masonandrewmann/MEAP/masons secret meap folder/Modulation/MEAP_Basic_FM/MEAP_Basic_FM.ino

/*
  Basic FM Patch
  
  Plays a constant sine wave at 440Hz modulates its frequency using another sine wave.
  Pot 1 controls the modulation oscillator's frequency.
  Pot 2 controls modulation depth.

  Mason Mann, CC0
 */

#include <MozziGuts.h>
#include <Oscil.h>
#include <mozzi_rand.h>
#include <mozzi_midi.h>
#include <Mux.h>
#include <SPI.h>
#include <tables/sin8192_int8.h> // loads sine wavetable

#define CONTROL_RATE 64 // Hz, powers of 2 are most reliable

using namespace admux;

Oscil<SIN8192_NUM_CELLS, AUDIO_RATE> carrierOsc(SIN8192_DATA);
Oscil<SIN8192_NUM_CELLS, AUDIO_RATE> modulatorOsc(SIN8192_DATA);

Q16n16 modDepth = 0;

// variables for potentiometers
int potVals[] = {0, 0};

void setup(){
  Serial.begin(115200);
  pinMode(34, INPUT);
  startMozzi(CONTROL_RATE);
  carrierOsc.setFreq(440); //set frequency of carrier oscillator
  modulatorOsc.setFreq(440); //set frequency of modulation oscillator
}


void loop(){
  audioHook();
}


void updateControl(){
  readPots(); // reads potentiometers
  modulatorOsc.setFreq((float)map(potVals[0], 0, 4095, 1, 1000)); // set mod oscillator range to 1->1000Hz
  modDepth = Q7n0_to_Q7n8(map(potVals[1], 0, 4095, 0, 127)); // convert mod depth to fixed point signed int between 0 and 127
}


int updateAudio(){
  Q15n16 modulation = modDepth * modulatorOsc.next() >> 8; // calculate mod depth in 15n16 signed int
  return MonoOutput::from8Bit(carrierOsc.phMod(modulation * 4)); // scale by factor of 4 and apply phase mod to carrier oscillator 
}

void readPots(){
  mozziAnalogRead(0);
  potVals[0] = mozziAnalogRead(39);
  
  mozziAnalogRead(1);
  potVals[1] = mozziAnalogRead(36);
}
