masonandrewmann/MEAP/Meap.h

/*
  Meap.h - Library accompanying MEAP boards.
  Created by Mason Mann, January 24, 2024.
*/
#ifndef MEAP_H_
#define MEAP_H_

#include "MozziConfigValues.h"
#define ESP_SAMPLE_SIZE 4 // 2 * sizeof(int16_t)

#ifndef MOZZI_AUDIO_RATE
#define MOZZI_AUDIO_RATE 32768
#endif

#ifndef MOZZI_CONTROL_RATE
#define MOZZI_CONTROL_RATE 64
#endif

#define MOZZI_AUDIO_MODE MOZZI_OUTPUT_EXTERNAL_CUSTOM
#define MOZZI_AUDIO_BITS 16
#define MOZZI_PDM_RESOLUTION 8

#ifndef MOZZI_AUDIO_CHANNELS
#define MOZZI_AUDIO_CHANNELS MOZZI_STEREO
#endif

#include "Arduino.h"
#include <Mozzi.h>

#include "driver/i2s_std.h"
// // I2S communication with SGTL5000 Audio Codec

#include <MIDI.h> // Arduino Midi library https://github.com/FortySevenEffects/arduino_midi_library

#include "Meap_classes.h"
// include all mozzi modules
#include <mozzi_midi.h>
#include <mozzi_fixmath.h>
#include <mozzi_rand.h>
#include <ADSR.h>
#include <AudioDelay.h>
#include <AudioDelayFeedback.h>
#include <AutoMap.h>
#include <AutoRange.h>
#include <CapPoll.h>
// #include <CircularBuffer.h> // not included because it causes a redeclaration error, should have an #ifdef clause like rest of modules
#include <ControlDelay.h>
#include <DCfilter.h>
#include <Ead.h>
#include <EventDelay.h>
#include <IntMap.h>
#include <Line.h>
#include <Metronome.h>
#include <ResonantFilter.h>
#include <Oscil.h>
#include <PDResonant.h>
#include <Phasor.h>
#include <Portamento.h>
#include <RCpoll.h>
#include <ReverbTank.h>
#include <RollingAverage.h>
#include <Sample.h>
#include <SampleHuffman.h>
#include <Smooth.h>
#include <StateVariable.h>
#include <WaveFolder.h>
#include <WavePacket.h>
#include <WavePacketSample.h>
#include <WaveShaper.h>

#include <meap_modules/tools/midi_notes.h>

// ---- dependencies ----
#include <dependencies/LinkedList/LinkedList.h>

// ---- meap extensions to mozzi objects ----
#include <meap_mozzi/mSample.h>
#include <meap_mozzi/mOscil.h>
#include <meap_mozzi/mPortamento.h>
#include <meap_mozzi/mEad.h>

// clutter
#include <meap_modules/clutter/mSampler.h>

// #include <meap_modules/clutter/mSamplerVoice.h>
// #include <meap_modules/clutter/mSamplerPoly.h>
// #include <meap_modules/clutter/mBasicFM.h>
// #include <meap_modules/clutter/mBasicFMPoly.h>
#include <meap_modules/clutter/mGrainGenerator.h>
#include <meap_modules/clutter/mGrainCloud.h>
#include <meap_modules/clutter/mSampleGrainGenerator.h>
#include <meap_modules/clutter/mSampleGrainCloud.h>
// #include <meap_modules/clutter/mGuitarPoly.h>
// #include <meap_modules/clutter/mFM2Voice.h>
// #include <meap_modules/clutter/mFM2Poly.h>
// #include <meap_modules/clutter/mWavetableSynth.h>
// #include <meap_modules/clutter/mOscBank.h>
// #include <meap_modules/clutter/mRealSamplerPoly.h>
// #include <meap_modules/clutter/mChopper.h>

// -------------------- MEAP DSP --------------------

// ---- TOOLS ----
#include <meap_modules/tools/fast_pow2.h>
#include <meap_modules/tools/mRandomDistribution.h>
#include <meap_modules/tools/mEventDelayMicros.h>
// #include <meap_modules/tools/mSD.h>
// #include <meap_modules/tools/mPlaySD16.h>
// #include <meap_modules/tools/mPlaySD8.h>

// ---- DSP ----
#include <meap_modules/dsp/mFIR.h>
#include <meap_modules/dsp/mIIR.h>
#include <meap_modules/dsp/mNaturalComb.h>
#include <meap_modules/dsp/mFeedbackComb.h>
#include <meap_modules/dsp/mFeedforwardComb.h>
#include <meap_modules/dsp/mNaturalComb.h>
#include <meap_modules/dsp/mOnePoleLPF.h>
#include <meap_modules/dsp/mSchroederAllpass.h>
#include <meap_modules/dsp/mDelayLine.h>
#include <meap_modules/dsp/mRingz.h>
#include <meap_modules/dsp/mResonz.h>

// ---- EFFECTS ----
#include <meap_modules/effects/mSchroederReverb.h>
#include <meap_modules/effects/mPlateReverb.h>
#include <meap_modules/effects/mDigitalDelay.h>
#include <meap_modules/effects/mBitcrusher.h>
#include <meap_modules/effects/mFlanger.h>
#include <meap_modules/effects/mChorus.h>
#include <meap_modules/effects/mAnalogDelay.h>
#include <meap_modules/effects/mBufferOverride.h>

// ---- GENERATORS ----
#include <meap_modules/generators/mSineLFO.h>
#include <meap_modules/generators/mOperator.h>
#include <meap_modules/generators/mDust.h>
#include <meap_modules/generators/mWavetable.h>
#include <meap_modules/generators/mNoise.h>
#include <meap_modules/generators/mEnvSection.h>
#include <meap_modules/generators/mEnvelope.h>

// ---- INSTRUMENTS ----

#include <meap_modules/instruments/mInstrument.h>

#include <meap_modules/instruments/mFM4Voice.h>
#include <meap_modules/instruments/mFM4Instrument.h>

#include <meap_modules/instruments/mSubSynthVoice.h>
#include <meap_modules/instruments/mSubSynthInstrument.h>

#include <meap_modules/instruments/mStringSynthVoice.h>
#include <meap_modules/instruments/mStringSynthInstrument.h>

#include <meap_modules/instruments/mStringVoice.h>
#include <meap_modules/instruments/mStringInstrument.h>

#include <meap_modules/instruments/mPopVoice.h>
#include <meap_modules/instruments/mPopInstrument.h>

#include <meap_modules/instruments/mMarimbaVoice.h>
#include <meap_modules/instruments/mMarimbaInstrument.h>

// #include <meap_modules/instruments/mSamplerInstrument.h>

// nonstandard instruments

#include <meap_modules/instruments/mDrumRack.h>

#include <meap_modules/instruments/mDrumRackInstrument.h>

#include <meap_modules/instruments/mRompler.h>

// ---- COMPOSITION ----

#include <meap_modules/composition/mMML.h>
#include <meap_modules/composition/mTransitionTable.h>

// ---- WINDOWS ----
// adapted from pippi https://git.sr.ht/~hecanjog/pippi
#include <windows/WIN_BART.h>
#include <windows/WIN_BLACK.h>
#include <windows/WIN_COS.h>
#include <windows/WIN_GAUSS.h>
#include <windows/WIN_GAUSSIN.h>
#include <windows/WIN_GAUSSOUT.h>
#include <windows/WIN_HAMM.h>
#include <windows/WIN_HANN.h>
#include <windows/WIN_HANNIN.h>
#include <windows/WIN_HANNOUT.h>
#include <windows/WIN_NONE.h>
#include <windows/WIN_PLUCKIN.h>
#include <windows/WIN_PLUCKOUT.h>
#include <windows/WIN_RSAW.h>
#include <windows/WIN_SAW.h>
#include <windows/WIN_SINC.h>
#include <windows/WIN_SINE.h>
#include <windows/WIN_SINEIN.h>
#include <windows/WIN_SINEOUT.h>
#include <windows/WIN_TRI.h>

const uint16_t *MEAP_WINDOWS[] = { //  20 windows
    WIN_BART_DATA,
    WIN_BLACK_DATA,
    WIN_COS_DATA,
    WIN_GAUSS_DATA,
    WIN_GAUSSIN_DATA,
    WIN_GAUSSOUT_DATA,
    WIN_HAMM_DATA,
    WIN_HANN_DATA,
    WIN_HANNIN_DATA,
    WIN_HANNOUT_DATA,
    WIN_NONE_DATA,
    WIN_PLUCKIN_DATA,
    WIN_PLUCKOUT_DATA,
    WIN_RSAW_DATA,
    WIN_SAW_DATA,
    WIN_SINC_DATA,
    WIN_SINE_DATA,
    WIN_SINEIN_DATA,
    WIN_SINEOUT_DATA,
    WIN_TRI_DATA};

// ---- WAVETABLES ----
#include <wavetables/WT_SAW.h>
#include <wavetables/WT_SINE.h>
#include <wavetables/WT_SQUARE.h>
#include <wavetables/WT_TRI.h>

i2s_chan_handle_t tx_handle;
i2s_chan_handle_t rx_handle;

// MOZZI output buffer
bool _esp32_can_buffer_next = true; // initialize to true
int16_t _esp32_prev_sample[2];

int16_t meap_input_frame[2];

inline bool esp32_tryWriteSample()
{
    size_t bytes_written;
    i2s_channel_write(tx_handle, &_esp32_prev_sample, 4, &bytes_written, 0); // 4 = 2 * sizeof(int16_t)
    return (bytes_written != 0);
}

inline void audioOutput(const AudioOutput f)
{
    _esp32_prev_sample[0] = f.l();
    _esp32_prev_sample[1] = f.r();

    _esp32_can_buffer_next = esp32_tryWriteSample();

    // audio input
    size_t bytes_read;
    i2s_channel_read(rx_handle, &meap_input_frame, 4, &bytes_read, 0);
}

inline bool canBufferAudioOutput()
{
    if (_esp32_can_buffer_next)
    {
        return true;
    }
    _esp32_can_buffer_next = esp32_tryWriteSample();
    return _esp32_can_buffer_next;
}

#endif // MEAP_H_
