masonandrewmann/MEAP/meap_modules/clutter/mFM2Poly.h

#ifndef MFM2POLY_H_
#define MFM2POLY_H_

#include <Meap.h>
#include <tables/sin8192_int8.h> // table for Oscils to play
#include <dependencies/LinkedList/LinkedList.h>

template <uint32_t mNUM_CELLS = SIN8192_NUM_CELLS, bool FILTER_ACTIVE = false, uint16_t mPOLYPHONY = 4, class T = int8_t>
class mFM2Poly
{
public:
    mFM2Poly(const int8_t *TABLE_NAME, uint8_t *midi_table_name)
    {
        init(TABLE_NAME, midi_table_name);
    };

    mFM2Poly(const int8_t *TABLE_NAME)
    {
        init(TABLE_NAME, NULL);
    };

    mFM2Poly()
    {
        init(SIN8192_DATA, NULL);
    }

    void init(const int8_t *TABLE_NAME, uint8_t *midi_table_name)
    {
        for (uint16_t i = 0; i < mPOLYPHONY; i++)
        {
            voices[i].init(TABLE_NAME);
            free_voices_.unshift(i); // add all voices to voice queue
        }
        curr_voice_ = 0;
        midi_table_name_ = midi_table_name;
        playing_ = false;

        message_type_ = 0;
        data1_ = 0;
        data2_ = 0;
        time_ = 0;

        pulse_counter_ = 0;
    }

    void begin()
    {
        // start_time = millis();
        stop();
        playing_ = true;
        current_midi_address_ = midi_table_name_;
        pulse_counter_ = 0;
        message_type_ = current_midi_address_[0];
        data1_ = current_midi_address_[1];
        data2_ = current_midi_address_[2];
        time_ = (current_midi_address_[3] << 8) + current_midi_address_[4];
    }

    void stop()
    {
        // send noteoffs to everything
        playing_ = false;
        for (uint16_t i = 0; i < mPOLYPHONY; i++)
        {
            voices[i].noteOff();
        }
        flush();
    }

    void updateMidi()
    {
        if (playing_)
        {
            pulse_counter_ += 1;
            while (pulse_counter_ >= time_)
            {
                switch (message_type_) // notes are indexed from 0 on sample_bank starting from C-1 (0)
                {
                case 0x80: // note off
                    noteOff(data1_);
                    break;
                case 0x90: // note on
                    if (data1_ != 127)
                    {
                        noteOn(data1_, data2_);
                    }
                    break;
                case 255: // end of file
                    playing_ = false;
                    return;
                    break;
                }
                current_midi_address_ += 5;
                pulse_counter_ = 0;
                message_type_ = current_midi_address_[0];
                data1_ = current_midi_address_[1];
                data2_ = current_midi_address_[2];
                time_ = (current_midi_address_[3] << 8) + current_midi_address_[4];
            }
        }
    }

    bool isPlaying()
    {
        return playing_;
    }

    void noteOn(uint16_t note, float vel)
    {
        if (free_voices_.size() > 0)
        {
            curr_voice_ = free_voices_.shift(); // remove head element and return it!
        }
        else
        {
            return; // no free voices, move along...
        }

        voices[curr_voice_].noteOn(note, vel);

        // store note in pressed notes queue
        MeapNoteAndVoice *my_note = new MeapNoteAndVoice;
        my_note->note_num = note;
        my_note->voice_num = curr_voice_;
        nonfree_voices_.add(my_note);
    }

    void noteOff(uint16_t note)
    {

        uint8_t num_nonfree_voices = nonfree_voices_.size();
        for (uint8_t i = 0; i < num_nonfree_voices; i++)
        {
            if (nonfree_voices_.get(i)->note_num == note)
            {
                uint8_t voice_num = nonfree_voices_.get(i)->voice_num; // voice num of note to turn off
                voices[voice_num].noteOff();
                free_voices_.add(voice_num);     // re-add voice to free queue
                delete (nonfree_voices_.get(i)); // delete voice from pressed queue
                nonfree_voices_.remove(i);       // remove freed voice from pressed queue
                return;
            }
        }
    }

    void flush()
    {
        nonfree_voices_.clear();
        free_voices_.clear();
        for (uint8_t i = 0; i < mPOLYPHONY; i++)
        {
            free_voices_.unshift(i); // add all voices to voice queue
            voices[i].noteOff();
        }
    }

    void setModADLevels(uint32_t a_l, uint32_t d_l)
    {
        for (uint16_t i = 0; i < mPOLYPHONY; i++)
        {
            voices[i].setModADLevels(a_l, d_l);
        }
    }

    void setCarrierADLevels(uint32_t a_l, uint32_t d_l)
    {
        for (uint16_t i = 0; i < mPOLYPHONY; i++)
        {
            voices[i].setCarrierADLevels(a_l, d_l);
        }
    }

    void setAlgorithm(int alg)
    {
        for (uint16_t i = 0; i < mPOLYPHONY; i++)
        {
            voices[i].setAlgorithm(alg);
        }
    }

    void setModTimes(uint32_t a_t, uint32_t d_t, uint32_t s_t, uint32_t r_t)
    {
        for (uint16_t i = 0; i < mPOLYPHONY; i++)
        {
            voices[i].setModTimes(a_t, d_t, s_t, r_t);
        }
    }

    void setCarrierTimes(uint32_t a_t, uint32_t d_t, uint32_t s_t, uint32_t r_t)
    {
        for (uint16_t i = 0; i < mPOLYPHONY; i++)
        {
            voices[i].setCarrierTimes(a_t, d_t, s_t, r_t);
        }
    }

    void setRatio(float mod_ratio)
    {
        for (uint16_t i = 0; i < mPOLYPHONY; i++)
        {
            voices[i].setRatio(mod_ratio);
        }
    }

    void setModTable(const T *TABLE_NAME)
    {
        for (uint16_t i = 0; i < mPOLYPHONY; i++)
        {
            voices[i].setModTable(TABLE_NAME);
        }
    }

    void setCarrierTable(const T *TABLE_NAME)
    {
        for (uint16_t i = 0; i < mPOLYPHONY; i++)
        {
            voices[i].setCarrierTable(TABLE_NAME);
        }
    }

    // 0-255
    void setFMAmount(int fm_amount)
    {
        for (uint16_t i = 0; i < mPOLYPHONY; i++)
        {
            voices[i].setFMAmount(fm_amount);
        }
    }

    void setCutoff(uint16_t cutoff_val)
    {
        for (uint16_t i = 0; i < mPOLYPHONY; i++)
        {
            voices[i].setCutoff(cutoff_val);
        }
    }

    void setResonance(uint16_t resonance_val)
    {
        for (uint16_t i = 0; i < mPOLYPHONY; i++)
        {
            voices[i].setResonance(resonance_val);
        }
    }

    void setFilterEnvAmount(uint16_t f_amt)
    {
        for (uint16_t i = 0; i < mPOLYPHONY; i++)
        {
            voices[i].setFilterEnvAmount(f_amt);
        }
    }

    void setFilterEnvTimes(uint32_t a_, uint32_t d_, uint32_t s_, uint32_t r_)
    {
        for (uint16_t i = 0; i < mPOLYPHONY; i++)
        {
            voices[i].setFilterEnvTimes(a_, d_, s_, r_);
        }
    }

    void setFilterAttackTime(uint32_t f_a)
    {
        for (uint16_t i = 0; i < mPOLYPHONY; i++)
        {
            voices[i].setFilterAttackTime(f_a);
        }
    }

    void setFilterDecayTime(uint32_t f_d)
    {
        for (uint16_t i = 0; i < mPOLYPHONY; i++)
        {
            voices[i].setFilterDecayTime(f_d);
        }
    }

    void setFilterReleaseTime(uint32_t f_r)
    {
        for (uint16_t i = 0; i < mPOLYPHONY; i++)
        {
            voices[i].setFilterReleaseTime(f_r);
        }
    }

    void setFilterSustainLevel(uint16_t level)
    {
        for (uint16_t i = 0; i < mPOLYPHONY; i++)
        {
            voices[i].setFilterSustainLevel(level);
        }
    }

    void setFilterType(uint16_t f_t)
    {
        for (uint16_t i = 0; i < mPOLYPHONY; i++)
        {
            voices[i].setFilterType(f_t);
        }
    }

    void update()
    {
        for (uint16_t i = 0; i < mPOLYPHONY; i++)
        {
            voices[i].update();
        }
    }

    int32_t next()
    {
        int32_t out_sample = 0;
        for (uint16_t i = 0; i < mPOLYPHONY; i++)
        {
            out_sample += voices[i].next();
        }

        return out_sample;
    }

    uint8_t *current_midi_address_;

    mFM2Voice<mNUM_CELLS, FILTER_ACTIVE, T> voices[mPOLYPHONY];

    // CLASS VARIABLES
    LinkedList<int16_t> free_voices_;
    LinkedList<MeapNoteAndVoice *> nonfree_voices_;

    uint16_t curr_voice_;

    // reading midi file
    uint8_t *midi_table_name_;

    uint64_t pulse_counter_;

    bool playing_;

    // last midi message
    uint8_t message_type_;
    uint8_t data1_;
    uint8_t data2_;
    uint16_t time_;
};

#endif // MFM2POLY_H_
