masonandrewmann/MEAP/masons secret meap folder/MARNIE/4YRS/MARNIE_D_4YRS/patterns.h

#define NUM_PATTERNS 8
#define NUM_DRUMS 8

int sample_pattern[NUM_PATTERNS][NUM_DRUMS][32] = 
  {
    {
      {1, 0, 0, 0, 1, 0, 0, 0,  1, 0, 0, 0, 1, 0, 0, 0,   1, 0, 0, 0, 1, 0, 0, 0,  1, 0, 0, 0, 1, 0, 0, 0},
      {0, 0, 0, 0, 1, 0, 0, 0,  0, 0, 0, 0, 1, 0, 0, 0,   0, 0, 0, 0, 1, 0, 0, 0,  0, 0, 0, 0, 1, 0, 0, 0},
      {0, 0, 1, 1, 0, 0, 1, 0,  0, 0, 1, 0, 0, 0, 1, 0,   0, 0, 1, 1, 0, 0, 1, 0,  0, 0, 1, 0, 0, 0, 1, 0},
      {0, 0, 0, 0, 0, 0, 0, 0,  0, 0, 0, 0, 0, 0, 0, 0,   0, 0, 0, 0, 0, 0, 0, 0,  0, 0, 0, 0, 0, 0, 0, 0},
      {0, 0, 0, 0, 0, 0, 0, 0,  0, 0, 0, 0, 0, 0, 1, 0,   0, 0, 0, 0, 0, 0, 0, 0,  0, 0, 0, 0, 0, 0, 1, 0},
      {0, 0, 0, 0, 0, 0, 0, 0,  0, 0, 0, 0, 0, 0, 0, 0,   0, 0, 0, 0, 0, 0, 0, 0,  0, 0, 0, 0, 0, 0, 0, 1},
      {0, 0, 0, 0, 0, 0, 0, 0,  0, 0, 0, 0, 0, 0, 0, 0,   0, 0, 0, 0, 0, 0, 0, 0,  0, 0, 0, 0, 0, 0, 0, 0},
      {0, 0, 0, 0, 0, 0, 0, 0,  0, 0, 0, 0, 0, 0, 0, 0,   0, 0, 0, 0, 0, 0, 0, 0,  0, 0, 0, 0, 0, 0, 0, 0},
    },

    {
      {1, 0, 0, 1, 0, 0, 0, 0,  1, 0, 1, 1, 0, 0, 0, 0,   1, 0, 0, 1, 0, 0, 0, 0,  1, 0, 1, 1, 0, 0, 0, 0},
      {0, 0, 0, 0, 1, 1, 0, 1,  0, 0, 0, 0, 1, 0, 1, 0,   0, 0, 0, 0, 1, 1, 0, 1,  0, 0, 0, 0, 1, 0, 1, 0},
      {0, 0, 1, 0, 1, 0, 1, 0,  1, 0, 1, 0, 1, 0, 1, 1,   0, 0, 1, 0, 1, 0, 1, 0,  1, 0, 1, 0, 1, 0, 1, 1},
      {0, 1, 0, 0, 0, 0, 0, 0,  0, 1, 0, 0, 0, 0, 0, 0,   0, 1, 0, 0, 0, 0, 0, 0,  0, 1, 0, 0, 0, 0, 0, 0},
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
      {0, 0, 0, 0, 0, 0, 0, 0,  0, 0, 0, 0, 1, 0, 0, 0,   0, 0, 0, 0, 0, 0, 0, 0,  0, 0, 0, 0, 1, 0, 0, 0},
      {0, 0, 0, 0, 0, 0, 0, 0,  0, 0, 0, 0, 0, 0, 0, 0,   0, 0, 0, 0, 0, 0, 0, 0,  0, 0, 0, 0, 0, 0, 0, 0},
    }
  };
