masonandrewmann/MEAP/meap_modules/instruments/mDrumRack.h

#ifndef MEAP_DRUMRACK_H_
#define MEAP_DRUMRACK_H_

#include <meap_mozzi/mSample.h>

template <uint64_t mMAX_SAMPLE_LENGTH, uint8_t mNUM_SAMPLES, class T = int8_t>
class mDrumRack
{
public:
    mDrumRack(const T **sample_list, uint32_t *sample_lengths, uint8_t *midi_table_name = NULL)
    {
        sample_list_ = sample_list;
        sample_lengths_ = sample_lengths;

        midi_table_name_ = midi_table_name;

        playing_ = false;

        message_type_ = 0;
        data1_ = 0;
        data2_ = 0;
        time_ = 0;

        pulse_counter_ = 0;

        default_freq_ = (float)AUDIO_RATE / (float)mMAX_SAMPLE_LENGTH;

        for (int i = mNUM_SAMPLES; --i >= 0;)
        {
            velocity_[i] = 32385; // 127 * 255
            sample_gain_[i] = 255;
            sample_bank_[i].setTable(sample_list_[i]);
            sample_bank_[i].setEnd(sample_lengths[i]);
            sample_bank_[i].setFreq(default_freq_);
        }

        if (sizeof(T) == sizeof(int16_t))
        {
            shift_val_ = 15; // 8 bits down for sample birate + 7 bits for velocity
        }
        else
        {
            shift_val_ = 7; // just 7 bits down for velocity
        }
    };
    void midiStart()
    {
        // start_time = millis();
        playing_ = true;
        current_address_ = midi_table_name_;
        pulse_counter_ = 0;
        message_type_ = current_address_[0];
        data1_ = current_address_[1];
        data2_ = current_address_[2];
        time_ = (current_address_[3] << 8) + current_address_[4];
    }

    void midiStop()
    {
        // stop all notes
        playing_ = false;
        for (int i = mNUM_SAMPLES; --i >= 0;)
        {
            sample_bank_[i].stop();
        }
    }

    void flush()
    {
        for (int i = mNUM_SAMPLES; --i >= 0;)
        {
            sample_bank_[i].stop();
        }
    }

    void updateMidi()
    {
        if (playing_)
        {
            pulse_counter_ += 1;
            while (pulse_counter_ >= time_)
            {

                switch (message_type_) // notes are indexed from 0 on sample_bank starting from C-1 (0)
                {
                // case 0x80: // note off
                //     break;
                case 0x90: // note on
                    if (data1_ != 127)
                    {
                        noteOn(data1_, data2_);
                    }
                    break;
                case 255: // end of file
                    playing_ = false;
                    return;
                    break;
                }
                pulse_counter_ = 0;

                current_address_ += 5;
                message_type_ = current_address_[0];
                data1_ = current_address_[1];
                data2_ = current_address_[2];
                time_ = (current_address_[3] << 8) + current_address_[4];
            }
        }
    }

    bool isPlaying()
    {
        return playing_;
    }

    void noteOn(uint16_t sample_num, int vel, float speed)
    {
        sample_bank_[sample_num].setFreq(speed * default_freq_);
        sample_bank_[sample_num].start();
        velocity_[sample_num] = vel * sample_gain_[sample_num];
    }

    void noteOn(uint16_t sample_num, int vel = 127)
    {
        sample_bank_[sample_num].start();
        velocity_[sample_num] = vel * sample_gain_[sample_num];
    }

    void noteOff(uint16_t sample_num)
    {
        sample_bank_[sample_num].stop();
    }

    void setSampleVolume(uint16_t sample_num, int volume)
    {
        sample_gain_[sample_num] = volume;
    }

    int32_t next()
    {
        uint64_t output_sample = 0;
        for (int i = mNUM_SAMPLES; --i >= 0;)
        {
            output_sample += (sample_bank_[i].next() * velocity_[i]) >> shift_val_;
        }
        return output_sample;
    }

    // CLASS VARIABLES

    mSample<mMAX_SAMPLE_LENGTH, AUDIO_RATE, T> sample_bank_[mNUM_SAMPLES];
    int velocity_[mNUM_SAMPLES];

    const T **sample_list_;
    uint32_t *sample_lengths_;
    int sample_gain_[mNUM_SAMPLES];

    uint8_t *midi_table_name_;
    uint8_t *current_address_;

    uint8_t shift_val_;

    // uint64_t start_time;
    uint64_t pulse_counter_;
    bool playing_;

    float default_freq_;

    // last midi message
    uint8_t message_type_;
    uint8_t data1_;
    uint8_t data2_;
    uint16_t time_;
};

#endif // MEAP_DRUMRACK_H_
