masonandrewmann/MEAP/masons secret meap folder/Samples/MEAP_Sample_Glitch/vocal_samp.h

#ifndef vocal_samp_H_
#define vocal_samp_H_
 
#if ARDUINO >= 100
#include "Arduino.h"
#else
#include "WProgram.h"
#endif
#include "mozzi_pgmspace.h"
 
#define vocal_samp_NUM_CELLS 36853
#define vocal_samp_SAMPLERATE 16384
 
CONSTTABLE_STORAGE(int8_t) vocal_samp_DATA [] = {-1, -1, -1, -1, -1, -1, -1, -1,
-1, -1, -1, -1, -1, -1, -1, -1, -1, -1, -1, -1, -1, -1, -1, -1, -1, -1, -1, -1,
-1, -1, -1, -1, -1, -1, -1, -1, -1, -1, -1, -1, -1, -1, -1, -1, -1, -1, 0, 0, 0,
0, 0, -1, -1, -1, -1, -1, -1, -1, -1, -1, -1, -1, -1, -1, -1, -1, -1, -1, 0, 0,
0, 0, -1, -1, -1, -1, -1, -1, -1, -1, -1, 0, 0, 0, 0, 0, 0, -1, 0, -1, 0, 0, -1,
-1, 0, 0, 0, -1, -1, -1, -1, -1, -1, -1, -1, -1, -1, -1, -1, -1, -1, -1, -1, -1,
-1, -1, -1, -1, -1, -1, -1, -1, -1, -1, -1, -1, -1, -1, -1, -1, -1, -1, -1, -1,
0, 0, 0, 0, 0, 0, 0, -1, -1, -1, -1, -1, -1, -1, -1, -1, -1, 0, -1, -1, -1, -1,
-1, -1, -1, -1, -1, -1, -1, 0, 0, 0, 0, 0, 0, 0, 0, 0, -1, -1, -1, 0, 0, 0, 0,
0, 0, 0, 0, 0, 0, 0, -1, -1, -1, -1, 0, 0, 0, 0, 0, 0, 0, 0, 0, 0, 0, 0, 0, 0,
0, 0, 0, 0, 0, 0, 0, 0, 0, 0, 0, -1, 0, 0, 0, 0, 0, 0, 0, 0, -1, -1, -1, 0, 0,
0, 0, 0, 0, 0, 0, -1, 0, -1, -1, -1, -1, -1, -1, -1, -1, -1, -1, -1, -1, -1, -1,
-1, -1, -1, -1, -1, -1, -1, -1, -1, -1, -1, -1, -1, -1, -1, -1, -1, -1, -1, 0,
-1, -1, -1, -1, -1, -1, -1, -1, -1, -1, -1, -1, -1, -1, -1, -1, -1, -1, -1, -1,
-1, -1, -1, -1, -1, -1, -1, -1, -1, -1, -1, -1, -1, -1, -1, -1, -1, -1, -1, -1,
-1, 0, -1, -1, -1, 0, 0, 0, -1, -1, -1, -1, -1, -1, -1, -1, 0, 0, 0, 0, 0, 0, 0,
0, 0, 0, 0, 0, 0, 0, 0, 0, 0, -1, 0, 0, 0, 0, 0, 0, 0, 0, 0, 0, 0, 0, 0, 0, 0,
0, 0, 0, 0, 0, 0, 0, 0, -1, 0, 0, 0, -1, -1, 0, 0, 0, 0, 0, 0, 0, 0, 0, 0, 0, 0,
-1, -1, -1, 0, -1, 0, 0, 0, -1, -1, -1, -1, -1, -1, -1, -1, -1, -1, -1, -1, -1,
-1, 0, 0, 0, -1, -1, -1, 0, -1, 0, 0, 0, 0, 0, 0, 0, 0, 0, 0, 0, 0, 0, 0, 0, 0,
0, 0, 0, 0, 0, 0, 0, 0, 0, 0, 0, 0, 0, 0, 0, 0, 0, 0, 0, 0, 0, 0, 0, 0, 0, 0, 0,
0, 0, 0, 0, 0, 0, 0, 0, 0, 0, 0, 0, 0, 0, 0, 0, 0, 0, -1, -1, -1, 0, -1, 0, -1,
-1, -1, -1, 0, 0, 0, -1, 0, 0, 0, 0, -1, 0, 0, 0, 0, 0, 0, 0, 0, 0, 0, 0, 0, 0,
0, 0, 0, 0, 0, 0, 0, 0, 0, 0, 0, 0, 0, 0, 0, 0, 0, 0, 0, 0, 0, 0, 0, 0, 0, 0, 0,
-1, -1, -1, -1, -1, -1, -1, -1, -1, -1, -1, -1, -1, -1, -1, -1, -1, -1, -1, -1,
-1, -1, -1, -1, -1, -1, -1, -1, -1, -1, -1, -1, -1, -1, -1, -1, 0, 0, 0, 0, 0,
0, 0, 0, 0, 0, 0, 0, 0, 1, 1, 1, 1, 1, 1, 1, 1, 1, 1, 1, 1, 1, 1, 0, 0, 0, 0, 0,
0, 0, 0, 0, -1, -1, -1, -1, -1, -1, -2, -2, -2, -2, -2, -2, -3, -3, -3, -3, -3,
-3, -3, -3, -3, -3, -3, -3, -3, -3, -3, -2, -2, -2, -1, -1, -1, -1, 0, 0, 0, 1,
1, 1, 1, 2, 2, 2, 3, 3, 3, 3, 3, 3, 3, 3, 3, 3, 3, 3, 3, 3, 2, 2, 2, 2, 1, 1, 1,
0, 0, -1, -1, -1, -2, -2, -2, -3, -3, -3, -4, -4, -4, -5, -5, -5, -6, -6, -6,
-6, -7, -7, -7, -7, -7, -7, -7, -6, -6, -5, -4, -2, -1, 0, 2, 3, 4, 5, 6, 7, 7,
7, 7, 7, 7, 7, 7, 6, 6, 6, 5, 5, 4, 4, 3, 3, 2, 2, 1, 1, 0, 0, 0, 0, -1, -1, -1,
-1, -1, -1, -1, -2, -2, -2, -2, -3, -3, -3, -4, -5, -5, -6, -6, -7, -8, -9, -10,
-10, -11, -11, -10, -9, -8, -6, -4, -2, 0, 2, 3, 4, 5, 5, 6, 6, 6, 6, 7, 7, 7,
7, 7, 7, 7, 7, 7, 6, 5, 5, 4, 3, 3, 2, 2, 2, 1, 1, 1, 1, 0, 0, -1, -1, -1, -1,
-2, -2, -2, -2, -2, -3, -3, -4, -5, -5, -6, -7, -8, -8, -9, -10, -11, -12, -12,
-12, -11, -9, -8, -6, -3, -1, 1, 3, 4, 6, 6, 6, 6, 6, 6, 5, 5, 5, 5, 5, 6, 7, 7,
7, 7, 6, 6, 5, 4, 4, 3, 3, 2, 2, 2, 2, 2, 2, 1, 1, 0, 0, 0, -1, -2, -2, -2, -2,
-3, -4, -4, -5, -6, -7, -8, -9, -9, -10, -11, -12, -13, -14, -14, -13, -11, -9,
-7, -4, -1, 2, 4, 6, 7, 8, 8, 8, 7, 6, 5, 5, 5, 4, 4, 4, 5, 6, 6, 6, 6, 6, 5, 5,
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

#endif /* vocal_samp_H_ */
