masonandrewmann/MEAP/masons secret meap folder/Samples/MEAP_Sample_Glitch_Duo/vocal_samp.h

#ifndef vocal_samp_H_
#define vocal_samp_H_
 
#if ARDUINO >= 100
#include "Arduino.h"
#else
#include "WProgram.h"
#endif
#include "mozzi_pgmspace.h"
 
#define vocal_samp_NUM_CELLS 38460
#define vocal_samp_SAMPLERATE 16384
 
CONSTTABLE_STORAGE(int8_t) vocal_samp_DATA [] = {-1, 0, -1, 0, -1, 0, 0, 0, -1,
-1, -1, -1, 0, -1, -1, -1, -1, 0, -1, 0, -1, -1, 0, -1, -1, -1, -1, -1, -1, -1,
-1, -1, -1, -1, -1, -1, -1, 0, 0, 0, 0, 0, 0, 0, -1, 0, -1, 0, -1, -1, -1, 0, 0,
0, 0, 0, 0, 0, 0, 0, 0, 0, 0, 0, 0, -1, -1, -1, -1, -1, 0, 0, 0, 0, 0, 0, 0, 0,
0, 0, 0, 0, 0, 0, 0, 0, 0, 0, 0, 0, 0, 0, 0, 0, 0, 0, 0, 0, 0, 0, 0, 0, 0, 0, 0,
0, 0, 0, 0, 0, 0, 0, 0, -1, -1, -1, -1, 0, 0, 0, 0, 0, 0, 0, 0, 0, 0, -1, 0, -1,
-1, -1, -1, -1, -1, -1, -1, -1, -1, -1, -1, -1, -1, -1, -1, -1, -1, -1, -1, -1,
-1, -1, -1, -1, -1, -1, -1, -1, -1, -1, -1, -1, -1, -1, -1, -1, -1, -1, -1, -1,
-1, 0, -1, -1, -1, -1, -1, -1, -1, -1, -1, -1, -1, -1, -1, -1, -1, -1, -1, -1,
-1, -1, -1, -1, -1, -1, -1, -1, -1, -1, -1, -1, -1, -1, -1, -1, -1, -1, -1, -1,
-1, -1, -1, -1, -1, -1, -1, -1, -1, -1, -1, -1, -1, -1, -1, -1, -1, 0, -1, -1,
0, -1, 0, -1, -1, -1, -1, -1, -1, -1, -1, -1, -1, 0, 0, 0, 0, 0, 0, 0, 0, 0, 0,
0, 0, 0, 0, 0, 0, 0, 0, 0, 0, 0, -1, -1, 0, -1, 0, 0, 0, 0, 0, 0, 0, 0, 0, 0, 0,
0, 0, 0, 0, 0, 0, 0, 0, 0, 0, 0, 0, 0, 0, 0, -1, -1, 0, 0, 0, -1, -1, -1, -1, 0,
0, 0, 0, 0, 0, 0, 0, 0, -1, 0, 0, -1, 0, -1, 0, -1, -1, 0, -1, 0, 0, 0, 0, -1,
-1, -1, -1, -1, -1, -1, -1, -1, -1, -1, -1, -1, -1, -1, -1, -1, -1, 0, -1, 0,
-1, -1, -1, -1, -1, -1, -1, -1, 0, 0, 0, 0, 0, 0, 0, 0, 0, 0, 0, 0, 0, 0, 0, 0,
0, 0, 0, 0, 0, 0, 0, 0, 0, 0, 0, 0, 0, 0, 0, 0, 0, 0, 0, 0, 0, 0, 0, 0, 0, 0, 0,
0, 0, 0, 0, 0, 0, 0, 0, 0, 0, 0, 0, 0, 0, 0, 0, 0, 0, 0, 0, 0, 0, 0, 0, 0, 0, 0,
0, 0, 0, 0, 0, -1, -1, -1, -1, -1, 0, -1, 0, 0, -1, 0, -1, -1, 0, 0, 0, 0, 0, 0,
0, 0, 0, 0, -1, 0, 0, 0, 0, 0, 0, 0, 0, 0, 0, 0, 0, 0, 0, 0, 0, 0, 0, 0, 0, 0,
0, 0, 0, 0, 0, 0, 0, 0, 0, 0, 0, 0, 0, 0, 0, 0, 0, 0, 0, 0, 0, 0, 0, 0, 0, 0, 0,
0, 0, 0, -1, -1, -1, -1, -1, -1, -1, -1, -1, -1, -1, -1, -1, -1, -1, -1, -1, -1,
-1, -1, -1, -1, -1, -1, -1, -1, -1, -1, -1, -1, -1, -1, -1, -1, -1, -1, -1, -1,
-1, -1, -1, -1, -1, -1, -1, 0, -1, 0, 0, 0, 0, 0, 0, 0, 0, 0, 0, 0, 0, 0, 0, 0,
1, 1, 1, 1, 1, 1, 1, 1, 1, 1, 1, 1, 1, 1, 1, 1, 1, 1, 0, 0, 0, 0, 0, 0, 0, 0, 0,
0, 0, -1, -1, -1, -1, -1, -1, -1, -2, -2, -2, -2, -2, -2, -2, -2, -3, -3, -3,
-3, -3, -3, -3, -3, -3, -3, -3, -3, -3, -3, -3, -3, -3, -3, -3, -2, -2, -2, -2,
-1, -1, -1, -1, -1, 0, 0, 0, 0, 1, 1, 1, 1, 2, 2, 2, 2, 3, 3, 3, 3, 3, 3, 3, 3,
3, 3, 3, 3, 3, 3, 3, 3, 3, 3, 2, 2, 2, 2, 2, 2, 1, 1, 1, 0, 0, 0, -1, -1, -1,
-2, -2, -2, -2, -3, -3, -3, -3, -4, -4, -4, -4, -5, -5, -5, -5, -6, -6, -6, -6,
-7, -7, -7, -7, -7, -7, -7, -7, -7, -7, -6, -6, -5, -4, -3, -2, -1, 1, 1, 3, 4,
4, 5, 6, 6, 7, 7, 7, 7, 7, 7, 7, 7, 7, 6, 6, 6, 6, 5, 5, 4, 4, 4, 3, 3, 2, 2, 2,
1, 1, 1, 0, 0, 0, 0, 0, -1, -1, -1, -1, -1, -1, -1, -1, -1, -2, -2, -2, -2, -3,
-3, -3, -3, -4, -4, -5, -5, -6, -6, -7, -7, -8, -9, -9, -10, -10, -11, -11, -11,
-10, -9, -8, -6, -5, -3, -2, 0, 1, 2, 3, 4, 5, 5, 6, 6, 6, 6, 6, 7, 7, 7, 7, 7,
7, 7, 8, 7, 7, 7, 7, 6, 6, 5, 4, 4, 3, 3, 2, 2, 2, 2, 1, 1, 1, 1, 1, 0, 0, 0,
-1, -1, -1, -1, -1, -2, -2, -2, -2, -2, -2, -3, -3, -4, -4, -5, -5, -6, -6, -7,
-8, -8, -9, -9, -10, -11, -11, -12, -12, -12, -11, -10, -9, -8, -6, -4, -2, 0,
1, 2, 4, 5, 6, 6, 6, 6, 6, 6, 6, 5, 5, 5, 5, 5, 5, 6, 6, 7, 7, 7, 7, 7, 6, 6, 5,
5, 4, 4, 3, 3, 2, 2, 2, 2, 2, 2, 2, 2, 1, 1, 1, 0, 0, 0, -1, -1, -2, -2, -2, -2,
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

#endif /* vocal_samp_H_ */
