masonandrewmann/MEAP/masons secret meap folder/MEAP_Demo/cmaj7.h

#ifndef myChord_H_
#define myChord_H_
 
#if ARDUINO >= 100
#include "Arduino.h"
#else
#include "WProgram.h"
#endif
#include "mozzi_pgmspace.h"
 
#define myChord_NUM_CELLS 87337
#define myChord_SAMPLERATE 16384
 
CONSTTABLE_STORAGE(int8_t) myChord_DATA [] = {0, 0, 0, 0, 0, 0, 0, 0, 0, 0, 0,
0, 0, 0, 0, 0, 0, 0, 0, 0, 0, 0, 0, 0, 0, 0, 0, 0, 0, 0, 0, 0, 0, 0, 0, 0, 0, 0,
0, 0, 0, 0, 0, 0, 0, 0, 0, 0, 0, 0, 0, 0, 0, 0, 0, 0, 0, 0, 0, 0, 0, 0, 0, 0, 0,
0, 0, 0, 0, 0, 0, 0, 0, 0, 0, 0, 0, 0, 0, 0, 0, 0, -1, -1, -1, -1, -1, -1, -1,
-1, -1, -1, -1, -1, -1, -1, -1, -1, -1, -1, -1, -1, -1, -1, -1, -1, -1, -1, -1,
-1, -1, -1, -1, -1, -1, -1, -1, -1, -1, -1, -1, -1, -2, -2, -2, -2, -1, -1, -2,
-2, -2, -2, -1, -1, -1, -1, -1, -1, -1, -1, -1, -1, -1, -1, -1, -1, -1, -1, -1,
-1, -1, -1, -1, -2, -2, -2, -2, -2, -2, -1, -2, -2, -2, -2, -2, -2, -2, -2, -2,
-2, -2, -2, -2, -2, -2, -1, -1, -1, -1, -1, -1, -1, -1, -1, -1, -1, -1, -1, -1,
-1, -1, 0, 0, 0, 0, 0, 0, 0, 0, 0, 0, 0, 0, 0, 0, 0, 0, 0, 0, 0, 0, 0, 0, 0, 0,
0, 0, 0, 0, 0, 0, 0, 0, 0, 1, 1, 0, 1, 1, 1, 1, 1, 1, 1, 1, 1, 1, 1, 1, 1, 1, 1,
1, 1, 1, 1, 1, 1, 1, 1, 1, 0, 0, 0, 0, 0, 0, 0, 0, 0, 0, 0, 0, 0, 0, 0, 0, 0, 1,
1, 1, 0, 1, 1, 0, 0, 1, 1, 1, 1, 0, 0, 0, 0, 1, 1, 1, 1, 0, 0, 1, 0, 0, 1, 1, 1,
1, 1, -1, -2, -2, -2, -2, -3, -5, -5, -5, -7, -7, -8, -10, -10, -10, -10, -11,
-12, -13, -12, -11, -12, -12, -10, -9, -8, -7, -6, -4, -2, 0, 2, 5, 8, 10, 12,
13, 15, 17, 18, 19, 21, 22, 22, 24, 25, 25, 26, 26, 27, 27, 27, 27, 26, 25, 24,
23, 22, 20, 19, 17, 15, 14, 13, 10, 8, 5, 2, 1, -1, -2, -4, -6, -6, -8, -9, -10,
-12, -14, -15, -16, -18, -19, -20, -21, -21, -22, -24, -25, -26, -27, -27, -27,
-27, -27, -27, -26, -25, -24, -24, -23, -22, -21, -20, -19, -18, -16, -14, -13,
-11, -10, -10, -10, -9, -9, -9, -8, -7, -5, -4, -3, -4, -6, -8, -10, -11, -12,
-14, -16, -17, -18, -21, -23, -23, -23, -23, -23, -24, -24, -24, -23, -23, -23,
-23, -22, -21, -19, -18, -17, -16, -15, -12, -9, -6, -2, 3, 8, 12, 17, 22, 26,
30, 34, 39, 43, 45, 48, 51, 53, 55, 56, 58, 59, 60, 60, 60, 60, 59, 59, 58, 57,
57, 56, 55, 54, 52, 51, 49, 46, 43, 41, 38, 34, 31, 27, 24, 21, 18, 14, 12, 9,
5, 1, -3, -7, -10, -12, -14, -18, -22, -25, -29, -32, -35, -37, -39, -40, -41,
-42, -43, -43, -43, -44, -44, -43, -43, -43, -43, -42, -41, -40, -39, -37, -35,
-33, -31, -30, -29, -29, -28, -25, -22, -20, -17, -16, -15, -15, -16, -17, -18,
-18, -19, -20, -21, -22, -24, -25, -26, -27, -29, -30, -30, -30, -31, -32, -33,
-32, -32, -31, -30, -29, -29, -29, -28, -27, -25, -23, -20, -16, -11, -7, -3, 1,
5, 10, 14, 19, 23, 27, 30, 33, 37, 40, 43, 46, 48, 51, 53, 54, 56, 58, 59, 61,
61, 62, 62, 63, 63, 62, 62, 61, 61, 60, 59, 58, 56, 54, 52, 49, 47, 45, 43, 41,
39, 35, 31, 27, 23, 20, 17, 15, 12, 9, 5, 1, -3, -7, -11, -14, -17, -20, -22,
-25, -27, -29, -31, -33, -35, -36, -37, -38, -38, -39, -39, -40, -39, -37, -36,
-35, -35, -34, -34, -35, -34, -33, -31, -29, -27, -27, -27, -27, -27, -27, -27,
-28, -28, -29, -29, -30, -32, -34, -35, -36, -36, -37, -38, -39, -40, -40, -40,
-39, -39, -38, -37, -35, -34, -34, -34, -33, -32, -30, -27, -24, -21, -18, -14,
-11, -7, -3, 1, 5, 9, 12, 16, 19, 21, 24, 28, 31, 33, 36, 38, 41, 43, 45, 47,
49, 51, 52, 53, 53, 54, 55, 55, 55, 55, 55, 56, 56, 56, 54, 52, 51, 51, 51, 50,
49, 48, 46, 43, 41, 39, 37, 35, 33, 31, 29, 26, 23, 19, 16, 13, 10, 8, 5, 2, -1,
-3, -5, -8, -10, -11, -12, -13, -15, -17, -18, -20, -20, -20, -20, -19, -19,
-19, -21, -22, -23, -23, -23, -23, -23, -23, -24, -25, -26, -28, -29, -31, -32,
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

#endif /* myChord_H_ */
