masonandrewmann/MEAP/examples/999_EXTRA_EXAMPLES/Micromontage/sample_includes.h

#include "samples/s1.h"
#include "samples/s2.h"
#include "samples/s3.h"
#include "samples/s4.h"
#include "samples/s5.h"
#include "samples/s6.h"
#include "samples/s7.h"
#include "samples/s8.h"
#include "samples/s9.h"
#include "samples/s10.h"
#include "samples/s11.h"
#include "samples/s12.h"
#include "samples/s13.h"
#include "samples/s14.h"
#include "samples/s15.h"
#include "samples/s16.h"
#include "samples/s17.h"
#include "samples/s18.h"
#include "samples/s19.h"
#include "samples/s20.h"
#include "samples/s21.h"
#include "samples/s22.h"
#include "samples/s23.h"
#include "samples/s24.h"
#include "samples/s25.h"
#include "samples/s26.h"
#include "samples/s27.h"
#include "samples/s28.h"
#include "samples/skick.h"




#define MICRO_NUM_SAMPLES 29

const int8_t *micro_list[MICRO_NUM_SAMPLES] = {
  s1_DATA,
  s2_DATA,
  s3_DATA,
  s4_DATA,
  s5_DATA,
  s6_DATA,
  skick_DATA,
  skick_DATA,
  s9_DATA,
  s10_DATA,
  s11_DATA,
  s12_DATA,
  s13_DATA,
  s14_DATA,
  s15_DATA,
  s16_DATA,
  s17_DATA,
  s18_DATA,
  s19_DATA,
  s20_DATA,
  s21_DATA,
  s22_DATA,
  s23_DATA,
  s24_DATA,
  s25_DATA,
  s26_DATA,
  s27_DATA,
  s28_DATA,
  skick_DATA,
};

uint32_t micro_lengths[MICRO_NUM_SAMPLES] = {
  s1_NUM_CELLS,
  s2_NUM_CELLS,
  s3_NUM_CELLS,
  s4_NUM_CELLS,
  s5_NUM_CELLS,
  s6_NUM_CELLS,
  skick_NUM_CELLS,
  skick_NUM_CELLS,
  s9_NUM_CELLS,
  s10_NUM_CELLS,
  s11_NUM_CELLS,
  s12_NUM_CELLS,
  s13_NUM_CELLS,
  s14_NUM_CELLS,
  s15_NUM_CELLS,
  s16_NUM_CELLS,
  s17_NUM_CELLS,
  s18_NUM_CELLS,
  s19_NUM_CELLS,
  s20_NUM_CELLS,
  s21_NUM_CELLS,
  s22_NUM_CELLS,
  s23_NUM_CELLS,
  s24_NUM_CELLS,
  s25_NUM_CELLS,
  s26_NUM_CELLS,
  s27_NUM_CELLS,
  s28_NUM_CELLS,
  skick_NUM_CELLS,
};
